kchatzif-uth/O4SIS/ΣΧΕΔΙΑ (RENDER)/ΚΑΤΟΨΗ.jpg

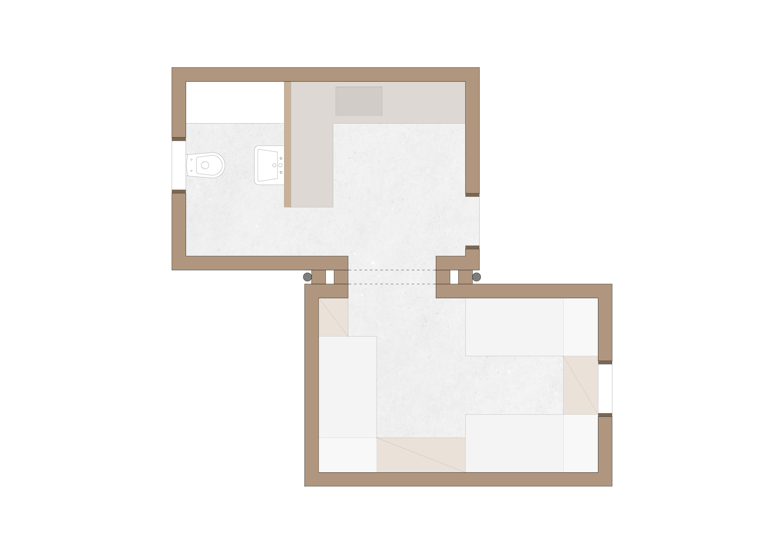
ΣΧΕΔΙΑ (RENDER)/ΚΑΤΟΨΗ.jpg
