kchatzif-uth/O4SIS/ΣΧΕΔΙΑ (RENDER)/ΟΨΗ β'.jpg

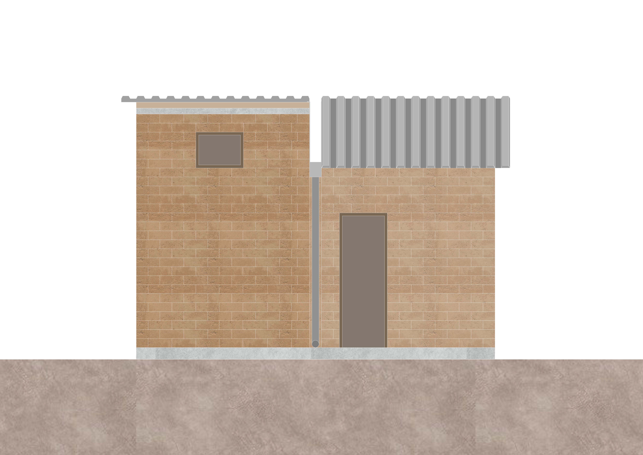
ΣΧΕΔΙΑ (RENDER)/ΟΨΗ β'.jpg
