kchatzif-uth/O4SIS/ΣΧΕΔΙΑ (RENDER)/ΤΟΜΗ Β-Β'.jpg

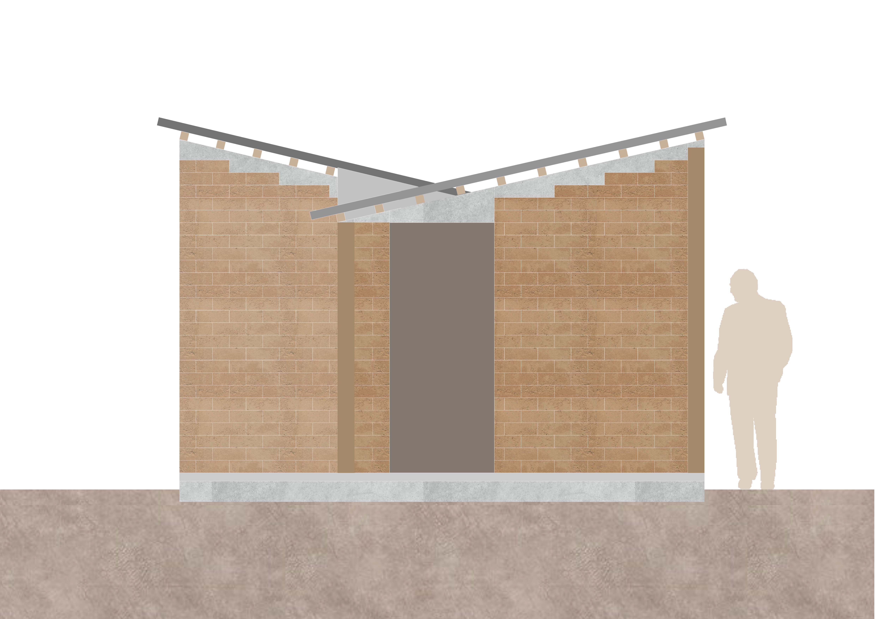
ΣΧΕΔΙΑ (RENDER)/ΤΟΜΗ Β-Β'.jpg
