kchatzif-uth/O4SIS/ΦΩΤΟΡΕΑΛΙΣΤΙΚΑ/1.png

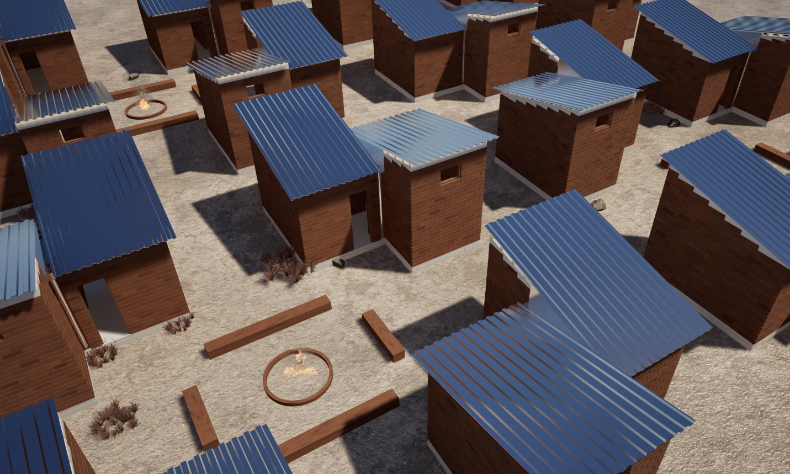
ΦΩΤΟΡΕΑΛΙΣΤΙΚΑ/1.png
