kchatzif-uth/O4SIS/ΦΩΤΟΡΕΑΛΙΣΤΙΚΑ/2.png

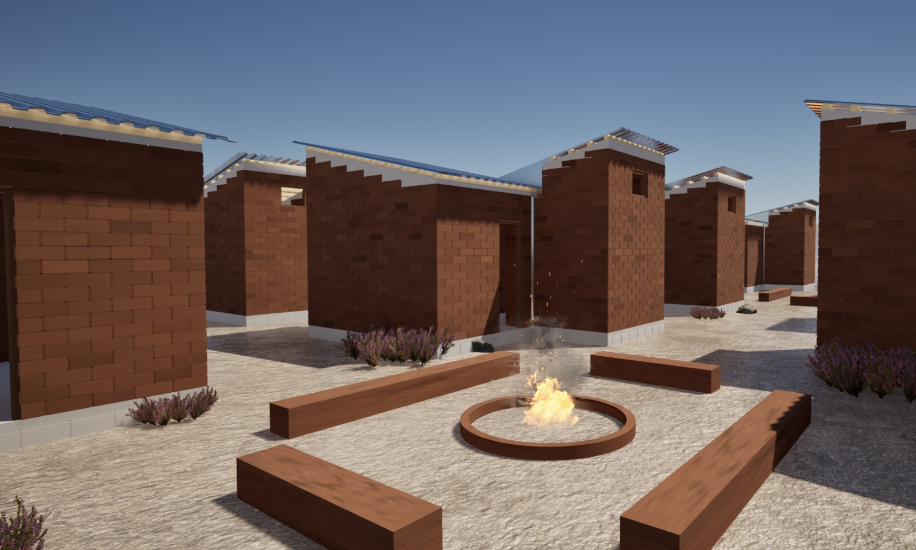
ΦΩΤΟΡΕΑΛΙΣΤΙΚΑ/2.png
