kchatzif-uth/O4SIS/ΦΩΤΟΡΕΑΛΙΣΤΙΚΑ/5.png

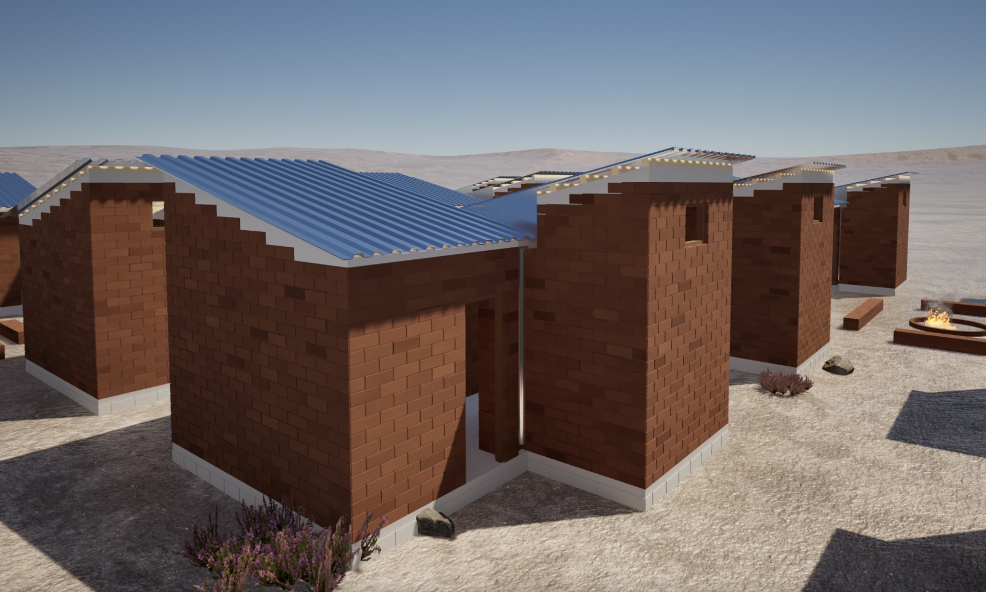
ΦΩΤΟΡΕΑΛΙΣΤΙΚΑ/5.png
